nipuni1313/Analog-Function-Generator/Images/WhatsApp Image 2023-12-06 at 09.40.14_6fe4c344.jpg

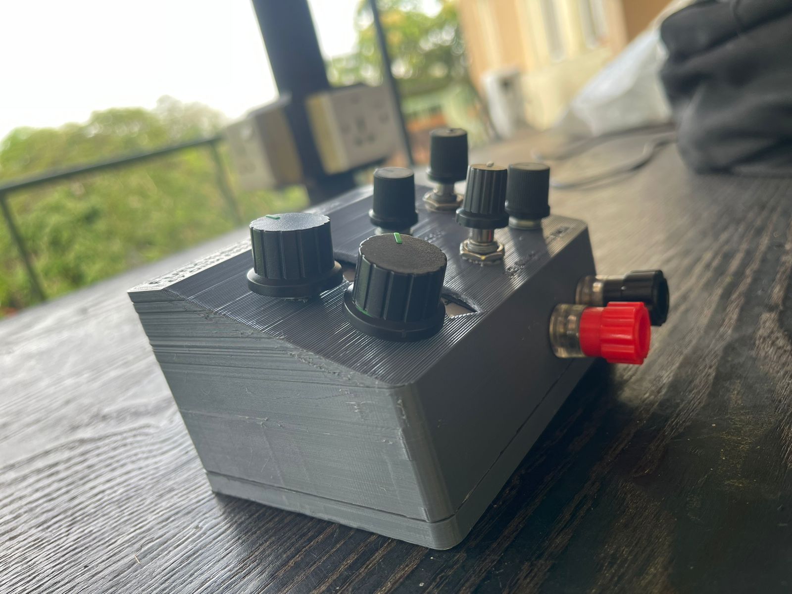
Images/WhatsApp Image 2023-12-06 at 09.40.14_6fe4c344.jpg
