nipuni1313/Analog-Function-Generator/Images/WhatsApp Image 2023-12-06 at 13.45.36_7bee3654.jpg

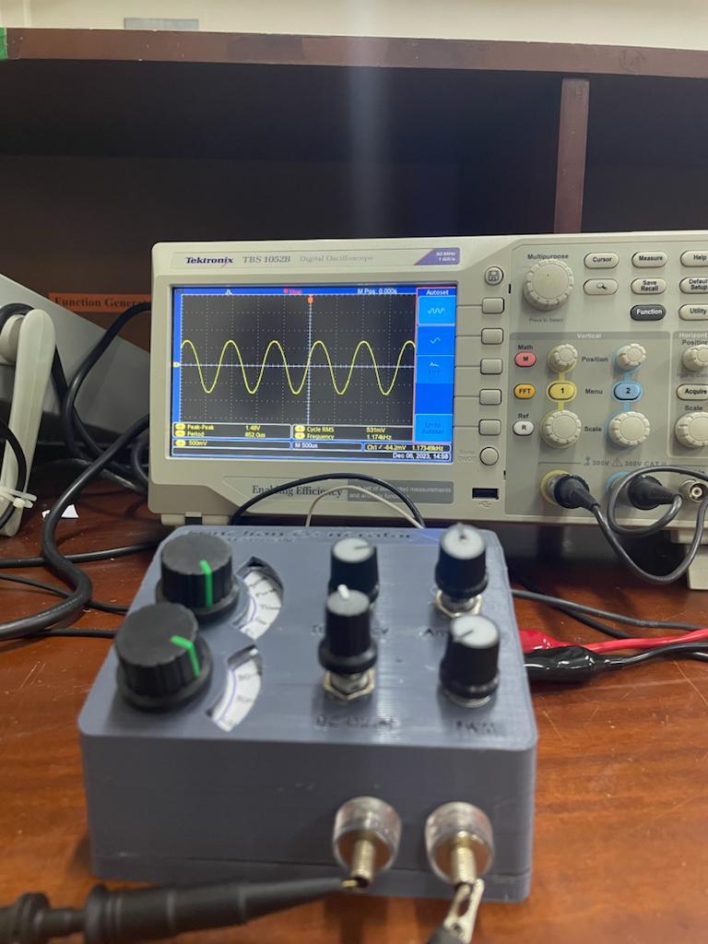
Images/WhatsApp Image 2023-12-06 at 13.45.36_7bee3654.jpg
