nipuni1313/Analog-Function-Generator/Images/WhatsApp Image 2023-12-06 at 13.48.49_f8270ae7.jpg

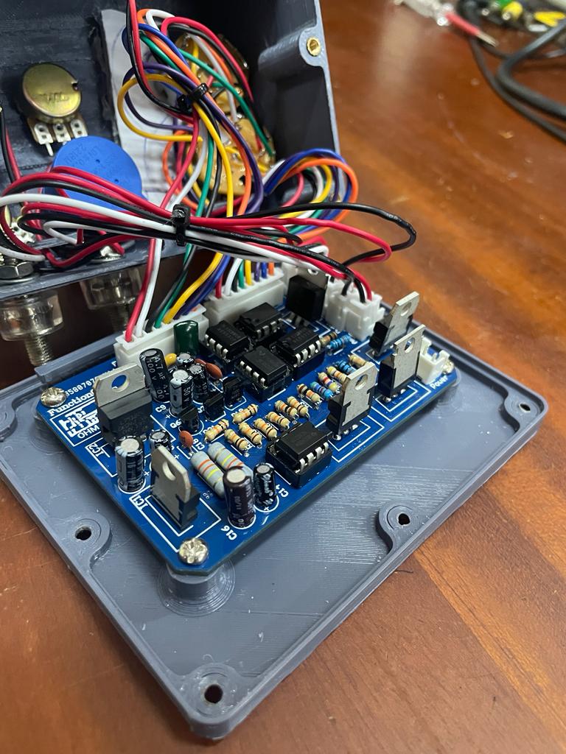
Images/WhatsApp Image 2023-12-06 at 13.48.49_f8270ae7.jpg
