nipuni1313/Analog-Function-Generator/Physical Implimentation/Breadboard Implementation.jpg

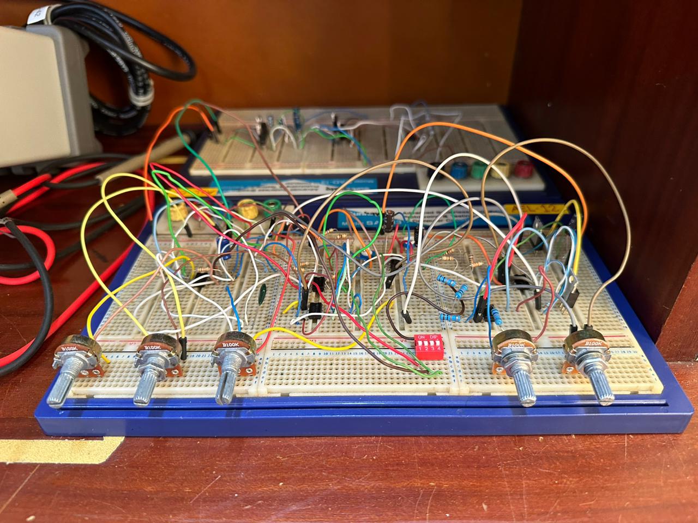
Physical Implimentation/Breadboard Implementation.jpg
