nipuni1313/Analog-Function-Generator/Physical Implimentation/Sinusoidal Wave.jpg

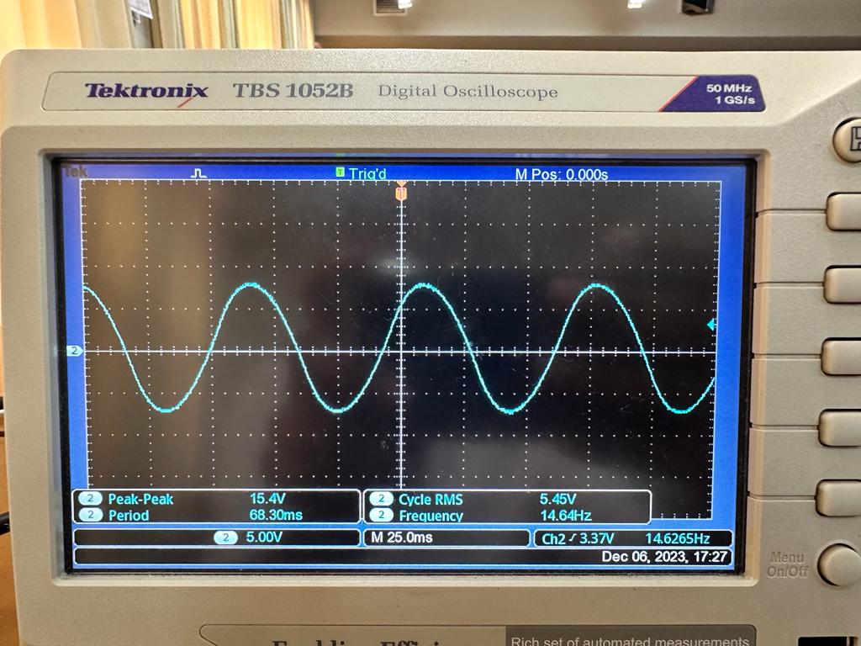
Physical Implimentation/Sinusoidal Wave.jpg
