nipuni1313/Analog-Function-Generator/Physical Implimentation/Square Wave.jpg

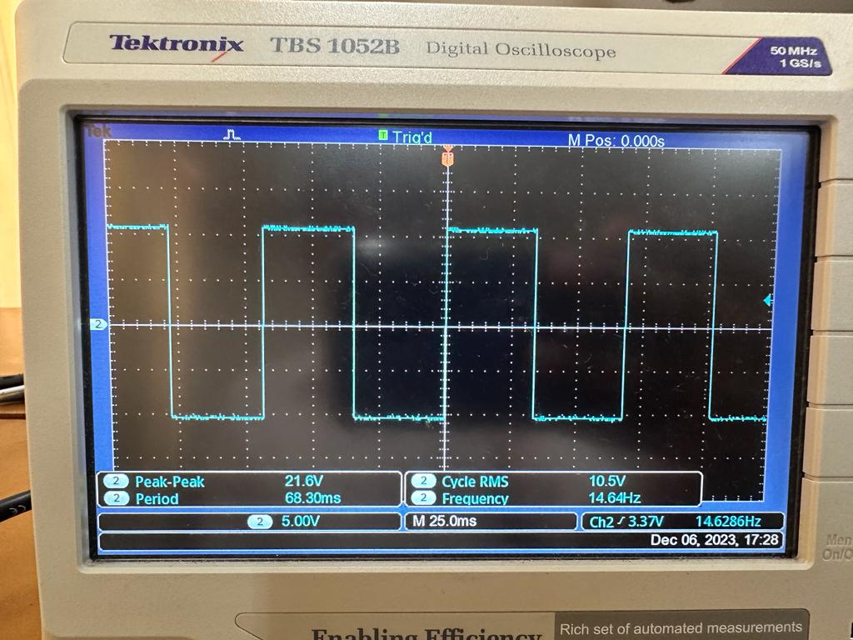
Physical Implimentation/Square Wave.jpg
