nipuni1313/Analog-Function-Generator/Physical Implimentation/Triangular Wave.jpg

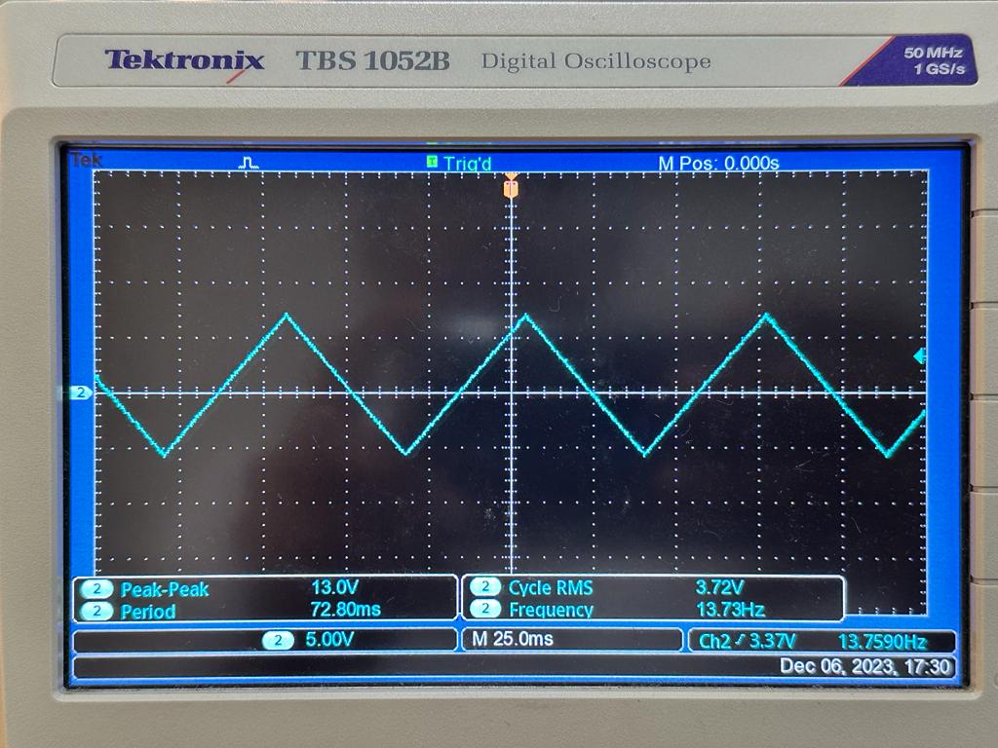
Physical Implimentation/Triangular Wave.jpg
